savvn001/STM32_FLIGHT_CONTROLLER/Src/usart.c

/**
  ******************************************************************************
  * File Name          : USART.c
  * Description        : This file provides code for the configuration
  *                      of the USART instances.
  ******************************************************************************
  * @attention
  *
  * <h2><center>&copy; Copyright (c) 2019 STMicroelectronics.
  * All rights reserved.</center></h2>
  *
  * This software component is licensed by ST under Ultimate Liberty license
  * SLA0044, the "License"; You may not use this file except in compliance with
  * the License. You may obtain a copy of the License at:
  *                             www.st.com/SLA0044
  *
  ******************************************************************************
  */

/* Includes ------------------------------------------------------------------*/
#include "usart.h"

/* USER CODE BEGIN 0 */
extern void UART_timeout();

/* USER CODE END 0 */

UART_HandleTypeDef huart6;

/* USART6 init function */

void MX_USART6_UART_Init(void)
{

  huart6.Instance = USART6;
  huart6.Init.BaudRate = 115200;
  huart6.Init.WordLength = UART_WORDLENGTH_8B;
  huart6.Init.StopBits = UART_STOPBITS_1;
  huart6.Init.Parity = UART_PARITY_NONE;
  huart6.Init.Mode = UART_MODE_TX;
  huart6.Init.HwFlowCtl = UART_HWCONTROL_NONE;
  huart6.Init.OverSampling = UART_OVERSAMPLING_16;
  if (HAL_UART_Init(&huart6) != HAL_OK)
  {
    Error_Handler();
  }

}

void HAL_UART_MspInit(UART_HandleTypeDef* uartHandle)
{

  GPIO_InitTypeDef GPIO_InitStruct = {0};
  if(uartHandle->Instance==USART6)
  {
    /* USART6 clock enable */
    __HAL_RCC_USART6_CLK_ENABLE();
  
    __HAL_RCC_GPIOC_CLK_ENABLE();
    /**USART6 GPIO Configuration    
    PC6     ------> USART6_TX
    PC7     ------> USART6_RX 
    */
    GPIO_InitStruct.Pin = GPIO_PIN_6|GPIO_PIN_7;
    GPIO_InitStruct.Mode = GPIO_MODE_AF_PP;
    GPIO_InitStruct.Pull = GPIO_PULLUP;
    GPIO_InitStruct.Speed = GPIO_SPEED_FREQ_VERY_HIGH;
    GPIO_InitStruct.Alternate = GPIO_AF8_USART6;
    HAL_GPIO_Init(GPIOC, &GPIO_InitStruct);

    /* USART6 interrupt Init */
    HAL_NVIC_SetPriority(USART6_IRQn, 11, 0);
    HAL_NVIC_EnableIRQ(USART6_IRQn);
  /* USER CODE BEGIN USART6_MspInit 1 */
    // Enable RX idle interrupt, which we use to handle variable-length messages
    __HAL_UART_ENABLE_IT(uartHandle, UART_IT_IDLE);
  /* USER CODE END USART6_MspInit 1 */
  }
}

void HAL_UART_MspDeInit(UART_HandleTypeDef* uartHandle)
{

  if(uartHandle->Instance==USART6)
  {
    /* Peripheral clock disable */
    __HAL_RCC_USART6_CLK_DISABLE();
  
    /**USART6 GPIO Configuration    
    PC6     ------> USART6_TX
    PC7     ------> USART6_RX 
    */
    HAL_GPIO_DeInit(GPIOC, GPIO_PIN_6|GPIO_PIN_7);

    /* USART6 interrupt Deinit */
    HAL_NVIC_DisableIRQ(USART6_IRQn);
  }
} 

/* USER CODE BEGIN 1 */
/**
  * @brief  UART receive process idle callback for short RX DMA transfers.
  * @param  huart: Pointer to a UART_HandleTypeDef structure that contains
  *                the configuration information for the specified UART module.
  * @retval None
  */
void HAL_UART_RxIdleCallback(UART_HandleTypeDef* huart)
{
  uint16_t rxXferCount = 0;
  if(huart->hdmarx != NULL)
  {
    DMA_HandleTypeDef *hdma = huart->hdmarx;

    /* Determine how many items of data have been received */
    rxXferCount = huart->RxXferSize - __HAL_DMA_GET_COUNTER(hdma);

    HAL_DMA_Abort(huart->hdmarx);

    huart->RxXferCount = 0;
    /* Check if a transmit process is ongoing or not */
    if(huart->gState == HAL_UART_STATE_BUSY_TX_RX)
    {
      huart->gState = HAL_UART_STATE_BUSY_TX;
    }
    else
    {
      huart->gState = HAL_UART_STATE_READY;
    }
  }

  UART_timeout();

}

/* USER CODE END 1 */

/************************ (C) COPYRIGHT STMicroelectronics *****END OF FILE****/
